Croionxx/VAF-clock/VAF_clock.kicad_pcb

## KiCad design docs/hardware/kicad/power_supply_v2/power_supply_v2.kicad_sch

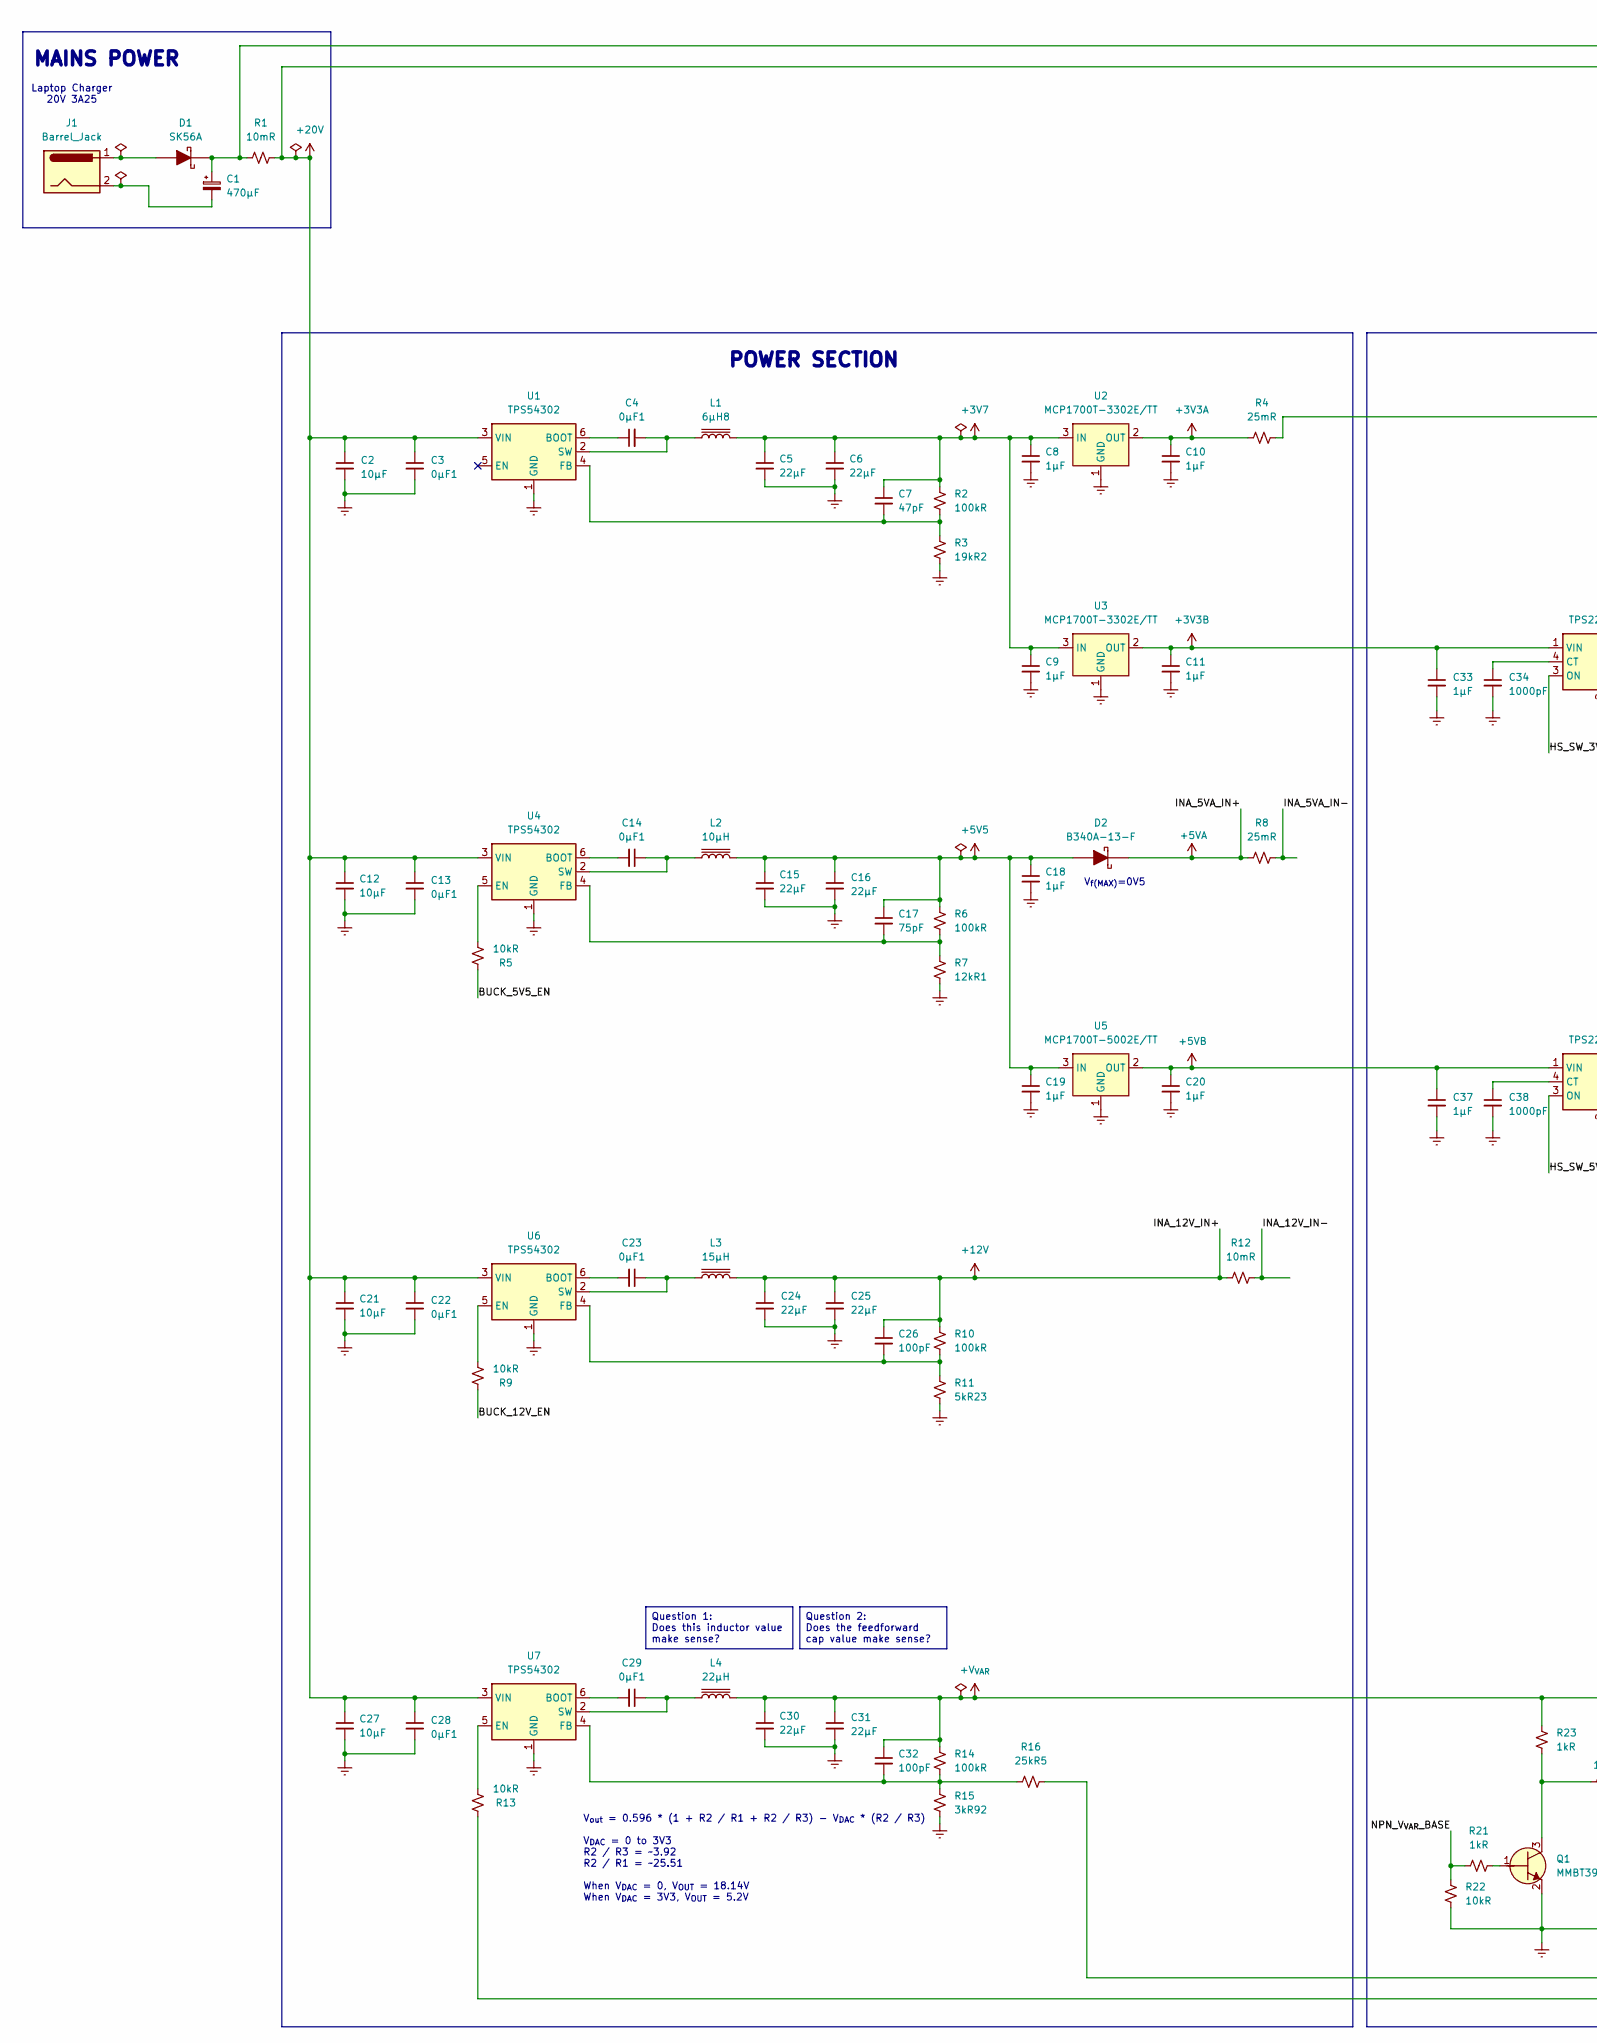
[picture p7: schematic power_supply_v2.kicad_sch, part in row 1, column 1]

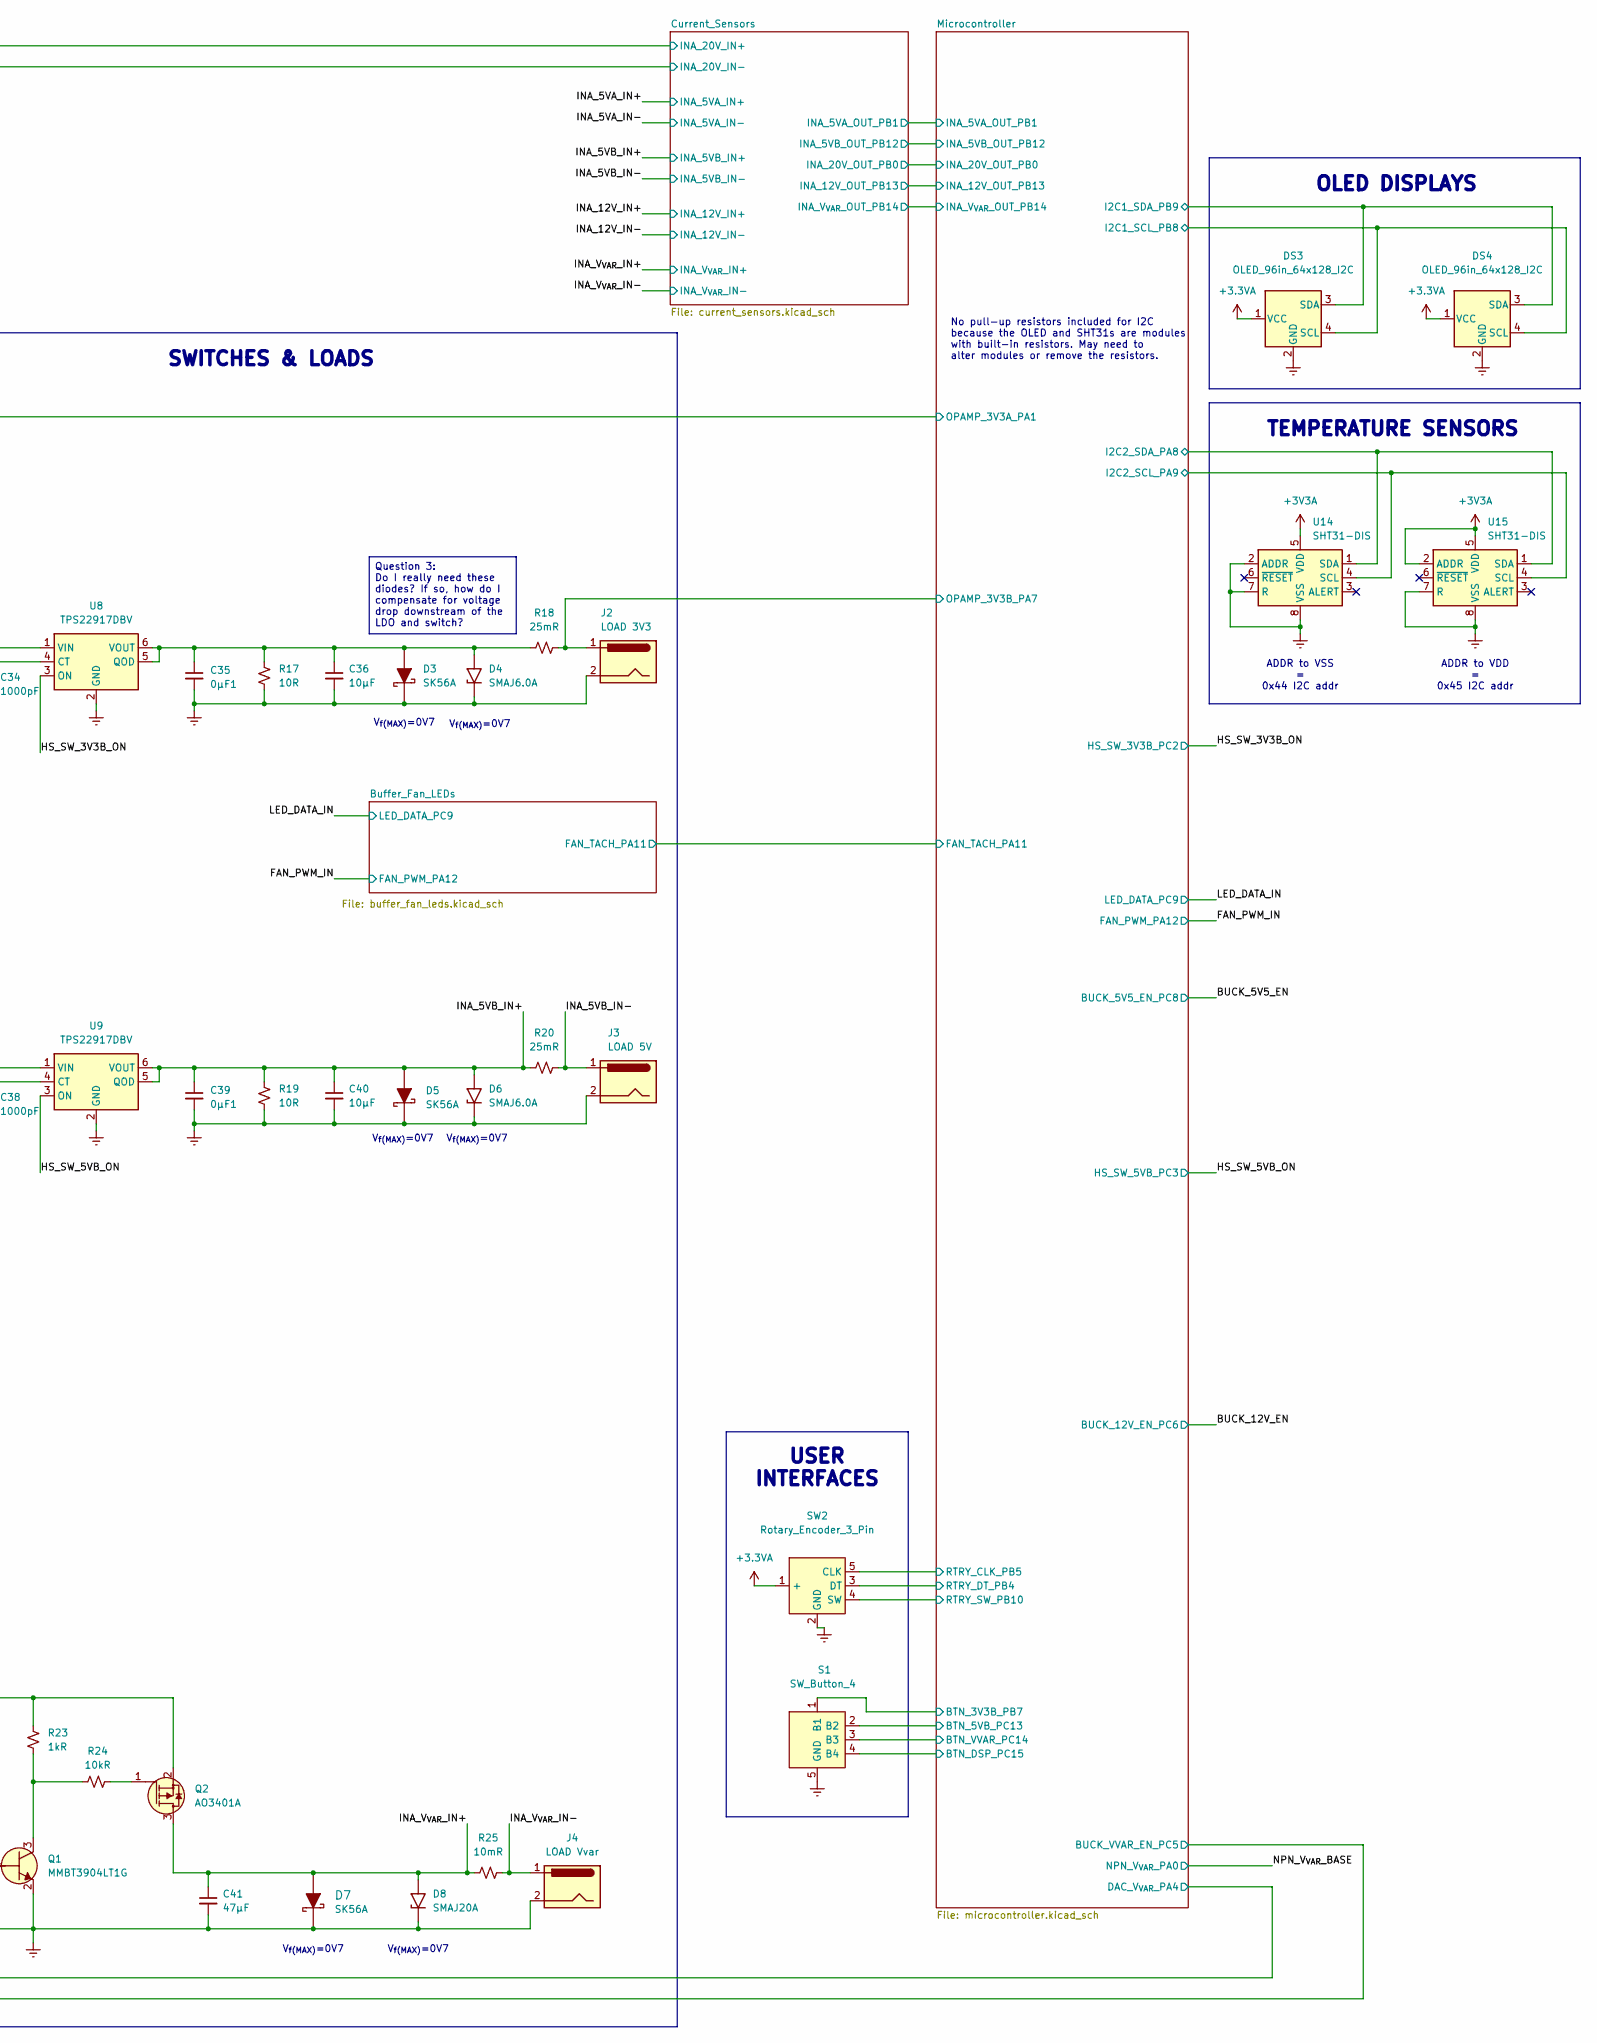
[picture p8: schematic power_supply_v2.kicad_sch, part in row 1, column 2]

Parts:
C1: 470μF
C2, C12, C21, C27, C36, C40: 10μF
C3, C4, C13, C14, C22, C23, C28, C29, C35, C39: 0μF1
C5, C6, C15, C16, C24, C25, C30, C31: 22μF
C7: 47pF
C8, C9, C10, C11, C18, C19, C20, C33, C37: 1μF
C17: 75pF
C26, C32: 100pF
C34, C38: 1000pF
C41: 47μF
D1, D3, D5, D7: SK56A; DO-214AC; MPN B340A-13-F; Digi-Key_PN B340A-FDICT-ND
D2: B340A-13-F; DO-214AC; MPN B340A-13-F; Digi-Key_PN B340A-FDICT-ND
D4, D6: SMAJ6.0A; D_SMA
D8: SMAJ20A; D_SMA
DS3, DS4: OLED_96in_64x128_I2C
J1: Barrel_Jack
J2: LOAD 3V3
J3: LOAD 5V
J4: LOAD Vvar
L1: 6μH8
L2: 10μH
L3: 15μH
L4: 22μH
Q1: MMBT3904LT1G; SOT-23-3; MPN MMBT3904LT1G; Digi-Key_PN MMBT3904LT1GOSCT-ND
Q2: AO3401A; SOT-23-3; MPN AO3401A; Digi-Key_PN 785-1001-1-ND
R1, R12, R25: 10mR
R2, R6, R10, R14: 100kR
R3: 19kR2
R4, R8, R18, R20: 25mR
R5, R9, R13, R22, R24: 10kR
R7: 12kR1
R11: 5kR23
R15: 3kR92
R16: 25kR5
R17, R19: 10R
R21, R23: 1kR
S1: (no value)
SW2: Rotary_Encoder_3_Pin
U1, U4, U6, U7: TPS54302; SOT-23-6
U2, U3: MCP1700T-3302E/TT; SOT-23-3; MPN MCP1700T-3302E/TT; Digi-Key_PN MCP1700T3302ETTCT-ND
U5: MCP1700T-5002E/TT; SOT-23-3; MPN MCP1700T-3302E/TT; Digi-Key_PN MCP1700T3302ETTCT-ND
U8, U9: TPS22917DBV; SOT-23-6
U14, U15: SHT31-DIS; Sensirion_DFN-8-1EP_2.5x2.5mm_P0.5mm_EP1.1x1.7mm

Connections:
+3.3VA: DS3.1 (VCC), DS4.1 (VCC), SW2.1 (+)
+3V3A: C10.1, R4.1, U2.2 (OUT), U14.5 (VDD), U15.2 (ADDR), U15.5 (VDD)
+3V3B: C11.1, C33.1, U3.2 (OUT), U8.1 (VIN)
+3V7: C5.1, C6.1, C7.1, C8.1, C9.1, L1.2, R2.1, U2.3 (IN), U3.3 (IN)
+5V5: C15.1, C16.1, C17.1, C18.1, C19.1, D2.A, L2.2, R6.1, U5.3 (IN)
+5VA: D2.K, R8.1
+5VB: C20.1, C37.1, U5.2 (OUT), U9.1 (VIN)
+12V: C24.1, C25.1, C26.1, L3.2, R10.1, R12.1
+20V: C2.1, C3.1, C12.1, C13.1, C21.1, C22.1, C27.1, C28.1, R1.2, U1.3 (VIN), U4.3 (VIN), U6.3 (VIN), U7.3 (VIN)
+V_{VAR}: C30.1, C31.1, C32.1, L4.2, Q2.2 (S), R14.1, R23.2
BTN_3V3B_PB7: S1.1 (B1)
BTN_5VB_PC13: S1.2 (B2)
BTN_DSP_PC15: S1.4 (B4)
BTN_VVAR_PC14: S1.3 (B3)
BUCK_5V5_EN: R5.2
BUCK_12V_EN: R9.2
BUCK_VVAR_EN_PC5: R13.2
DAC_V_{VAR}_PA4: R16.2
GNDREF: C2.2, C3.2, C5.2, C6.2, C8.2, C9.2, C10.2, C11.2, C12.2, C13.2, C15.2, C16.2, C18.2, C19.2, C20.2, C21.2, C22.2, C24.2, C25.2, C27.2, C28.2, C30.2, C31.2, C33.2, C34.2, C35.2, C36.2, C37.2, C38.2, C39.2, C40.2, C41.2, D3.K, D4.1 (A1), D5.K, D6.1 (A1), D7.K, D8.1 (A1), DS3.2 (GND), DS4.2 (GND), J2.2, J3.2, J4.2, Q1.2 (E), R3.2, R7.2, R11.2, R15.2, R17.2, R19.2, R22.1, S1.5 (GND), SW2.2 (GND), U1.1 (GND), U2.1 (GND), U3.1 (GND), U4.1 (GND), U5.1 (GND), U6.1 (GND), U7.1 (GND), U8.2 (GND), U9.2 (GND), U14.2 (ADDR), U14.7 (R), U14.8 (VSS), U14.9 (VSS), U15.7 (R), U15.8 (VSS), U15.9 (VSS)
HS_SW_3V3B_ON: U8.3 (ON)
HS_SW_5VB_ON: U9.3 (ON)
I2C1_SCL_PB8: DS3.4 (SCL), DS4.4 (SCL)
I2C1_SDA_PB9: DS3.3 (SDA), DS4.3 (SDA)
I2C2_SCL_PA9: U14.4 (SCL), U15.4 (SCL)
I2C2_SDA_PA8: U14.1 (SDA), U15.1 (SDA)
INA_5VA_IN-: R8.2
INA_5VB_IN+: C39.1, C40.1, D5.A, D6.2 (A2), R19.1, R20.1, U9.5 (QOD), U9.6 (VOUT)
INA_5VB_IN-: J3.1, R20.2
INA_12V_IN-: R12.2
INA_20V_IN+: C1.1, D1.K, R1.1
INA_V_{VAR}_IN+: C41.1, D7.A, D8.2 (A2), Q2.3 (D), R25.1
INA_V_{VAR}_IN-: J4.1, R25.2
NPN_V_{VAR}_BASE: R21.2, R22.2
unnamed: C1.2, J1.2
unnamed: C4.1, U1.6 (BOOT)
unnamed: C4.2, L1.1, U1.2 (SW)
unnamed: C7.2, R2.2, R3.1, U1.4 (FB)
unnamed: C14.1, L2.1, U4.2 (SW)
unnamed: C14.2, U4.6 (BOOT)
unnamed: C17.2, R6.2, R7.1, U4.4 (FB)
unnamed: C23.1, L3.1, U6.2 (SW)
unnamed: C23.2, U6.6 (BOOT)
unnamed: C26.2, R10.2, R11.1, U6.4 (FB)
unnamed: C29.1, L4.1, U7.2 (SW)
unnamed: C29.2, U7.6 (BOOT)
unnamed: C32.2, R14.2, R15.1, R16.1, U7.4 (FB)
unnamed: C34.1, U8.4 (CT)
unnamed: C35.1, C36.1, D3.A, D4.2 (A2), R17.1, R18.1, U8.5 (QOD), U8.6 (VOUT)
unnamed: C38.1, U9.4 (CT)
unnamed: D1.A, J1.1
unnamed: Q1.1 (B), R21.1
unnamed: Q1.3 (C), R23.1, R24.2
unnamed: Q2.1 (G), R24.1
unnamed: R5.1, U4.5 (EN)
unnamed: R9.1, U6.5 (EN)
unnamed: R13.1, U7.5 (EN)
OPAMP_3V3A_PA1: R4.2
OPAMP_3V3B_PA7: J2.1, R18.2
RTRY_CLK_PB5: SW2.5 (CLK)
RTRY_DT_PB4: SW2.3 (DT)
RTRY_SW_PB10: SW2.4 (SW)

Notes on the sheet:
V_{out} = 0.596 * (1 + R2 / R1 + R2 / R3) - V_{DAC} * (R2 / R3) V_{DAC} = 0 to 3V3 R2 / R3 = ~3.92 R2 / R1 = ~25.51 When V_{DAC} = 0, V_{OUT} = 18.14V When V_{DAC} = 3V3, V_{OUT} = 5.2V
V_{f(MAX)}=0V7
SWITCHES & LOADS
V_{f(MAX)}=0V5
USER INTERFACES
POWER SECTION
OLED DISPLAYS
Laptop Charger 20V 3A25
ADDR to VSS = 0x44 I2C addr
No pull-up resistors included for I2C because the OLED and SHT31s are modules with built-in resistors. May need to alter modules or remove the resistors.
MAINS POWER
ADDR to VDD = 0x45 I2C addr
TEMPERATURE SENSORS
Question 2: Does the feedforward cap value make sense?
Question 1: Does this inductor value make sense?
Question 3: Do I really need these diodes? If so, how do I compensate for voltage drop downstream of the LDO and switch?
